carsontpeters-rgb/Racing-Sim/Cad Files/Assemblys/Stick (1).step

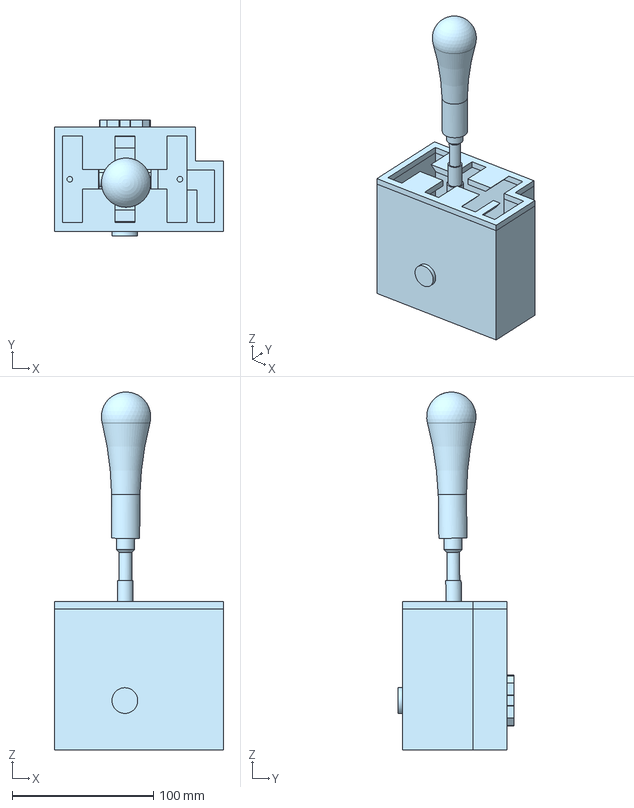
[picture p20: CAD file, 2026-03-14]
Cad Files/Assemblys/Stick (1).step
120.0 x 82.2 x 253.5 mm
