carsontpeters-rgb/Racing-Sim/Cad Files/Control panel/Knobs.step

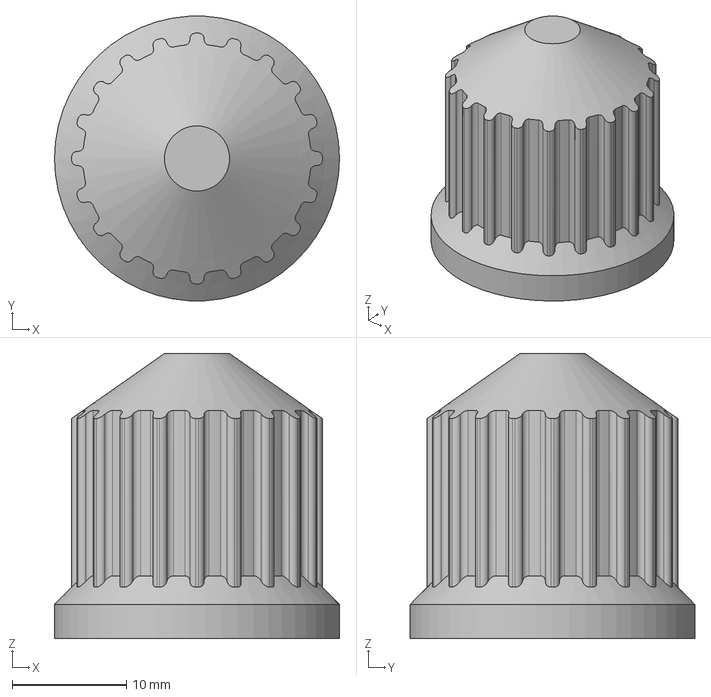
[picture p21: CAD file, 2026-03-14]
Cad Files/Control panel/Knobs.step
25.0 x 25.0 x 25.0 mm
