carsontpeters-rgb/Racing-Sim/Cad Files/Electronics/Rotery encoders.step

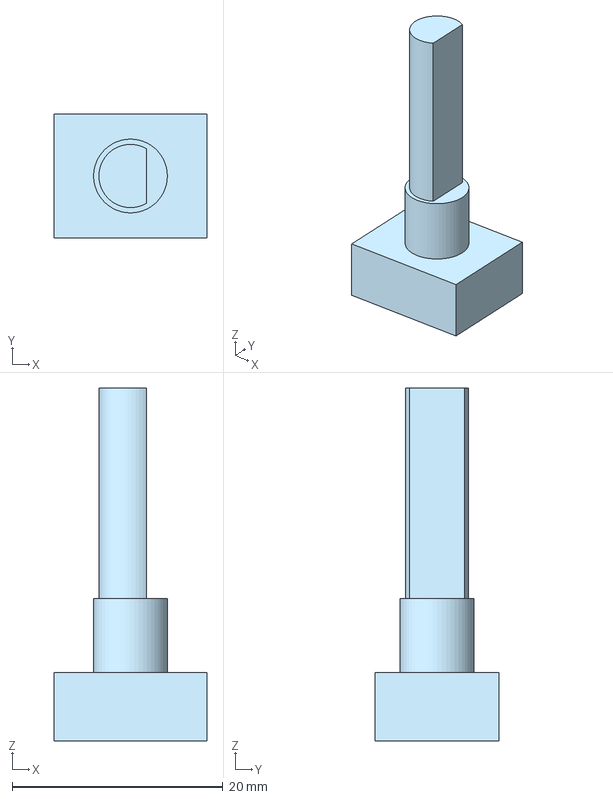
[picture p22: CAD file, 2026-03-14]
Cad Files/Electronics/Rotery encoders.step
14.5 x 11.8 x 33.5 mm
