carsontpeters-rgb/Racing-Sim/Cad Files/None Printed Parts/spring base Mount rod.step

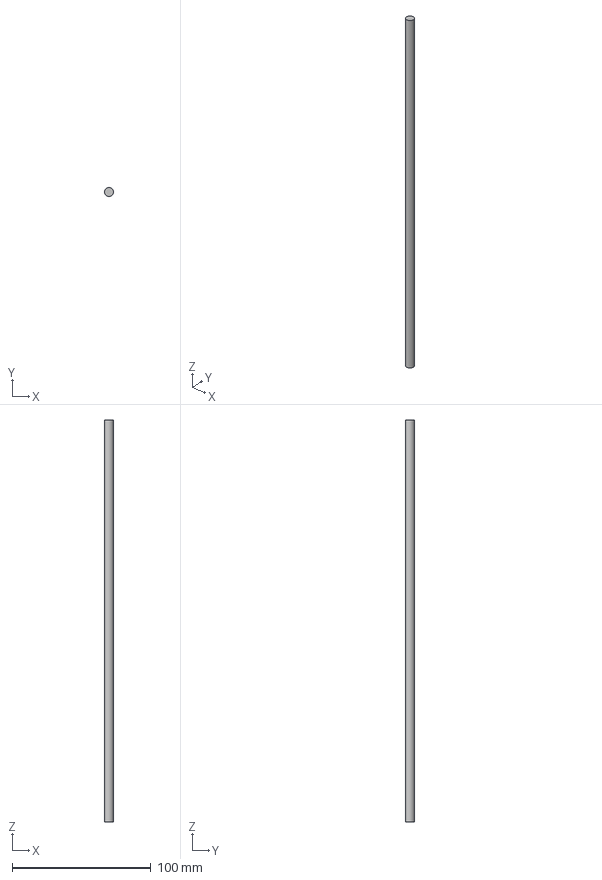
[picture p23: CAD file, 2026-03-14]
Cad Files/None Printed Parts/spring base Mount rod.step
6.49 x 6.50 x 290.0 mm
