carsontpeters-rgb/Racing-Sim/Cad Files/Pedals/Gas, Clutch and Break Pedal.step

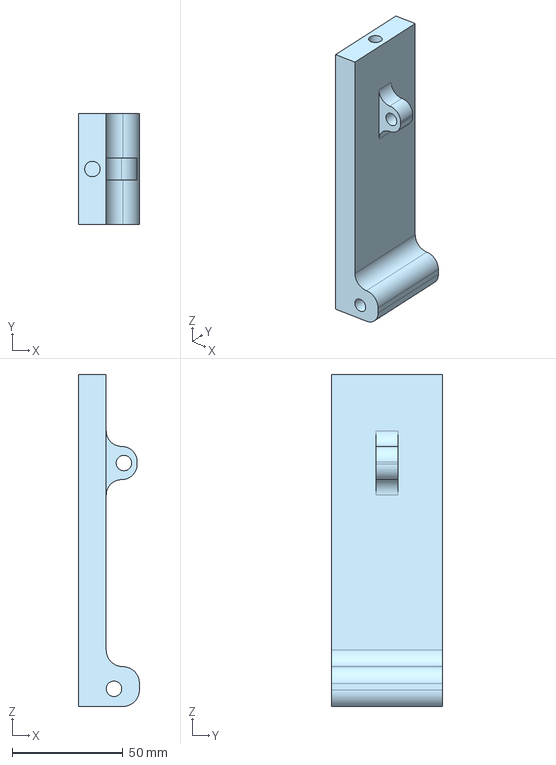
[picture p24: CAD file, 2026-03-14]
Cad Files/Pedals/Gas, Clutch and Break Pedal.step
27.5 x 50.0 x 150.0 mm
