carsontpeters-rgb/Racing-Sim/Cad Files/Shifter/X-AXIS.step

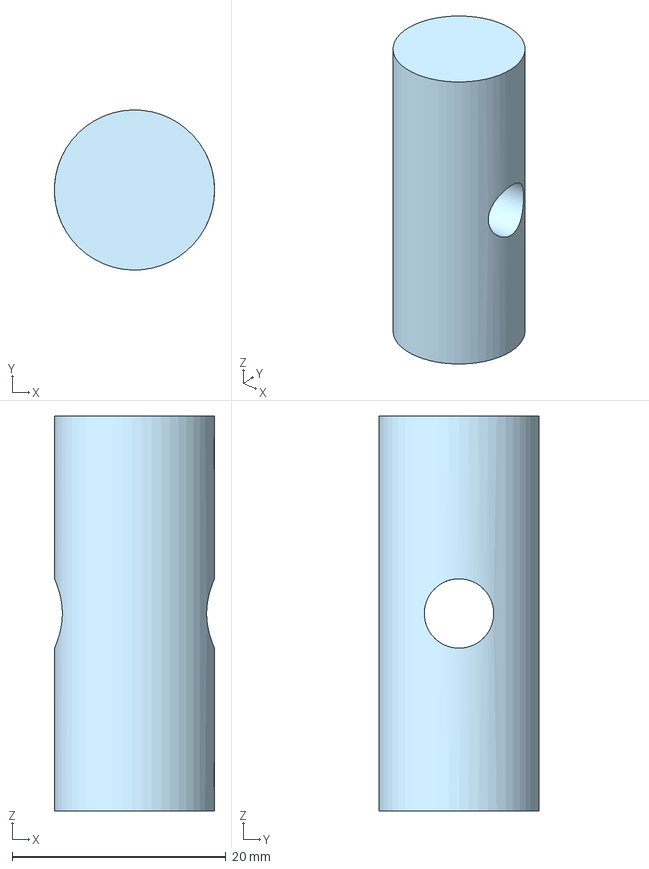
[picture p25: CAD file, 2026-03-14]
Cad Files/Shifter/X-AXIS.step
15.0 x 15.0 x 37.0 mm
