carsontpeters-rgb/Racing-Sim/Cad Files/Steering Wheel/Wheel gear.step

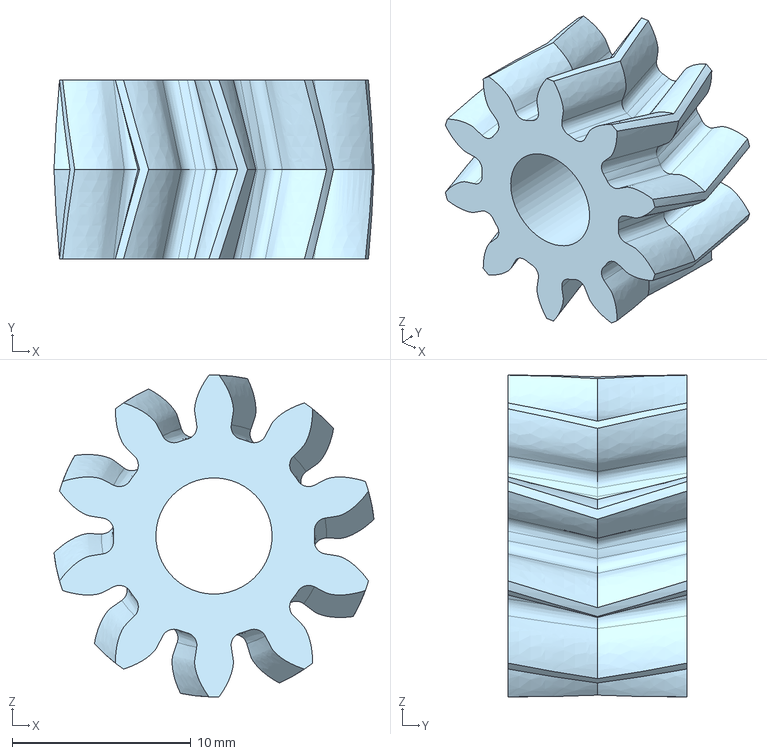
[picture p26: CAD file, 2026-03-14]
Cad Files/Steering Wheel/Wheel gear.step
17.9 x 10.0 x 18.0 mm
