carsontpeters-rgb/Racing-Sim/Cad Files/Assemblys/Pedals.step

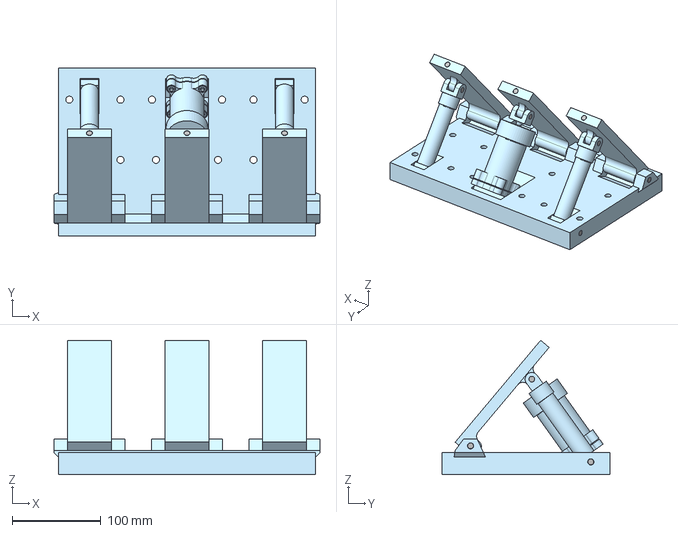
[picture p27: CAD file, 2026-03-14]
Cad Files/Assemblys/Pedals.step
300.0 x 190.0 x 151.6 mm
