carsontpeters-rgb/Racing-Sim/Cad Files/Electronics/Load Cell.step

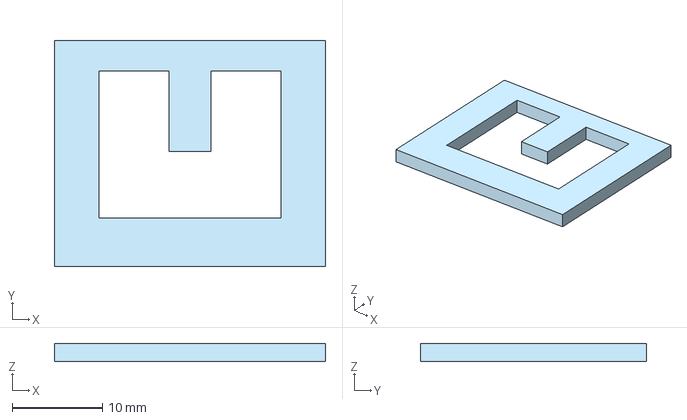
[picture p28: CAD file, 2026-03-14]
Cad Files/Electronics/Load Cell.step
30.0 x 25.0 x 2.00 mm
