carsontpeters-rgb/Racing-Sim/Cad Files/None Printed Parts/Pedal core rod.step

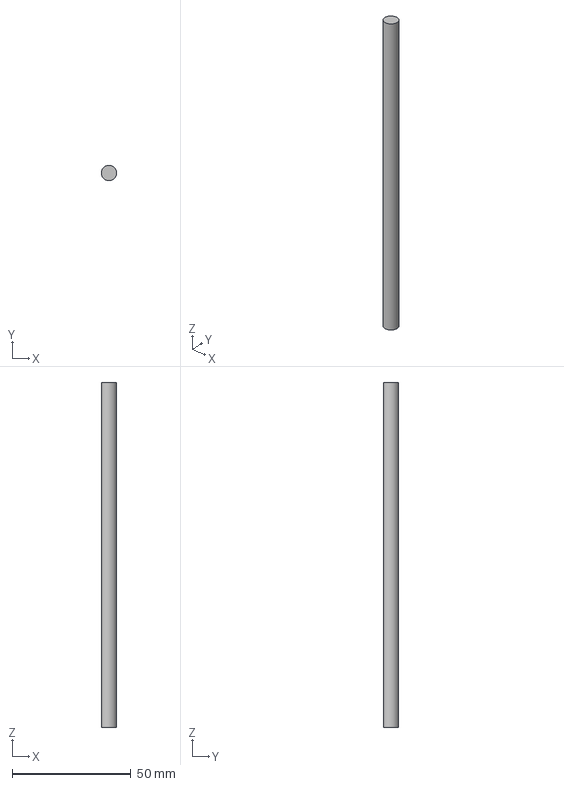
[picture p29: CAD file, 2026-03-14]
Cad Files/None Printed Parts/Pedal core rod.step
6.49 x 6.50 x 145.0 mm
