carsontpeters-rgb/Racing-Sim/Cad Files/Pedals/Cover.step

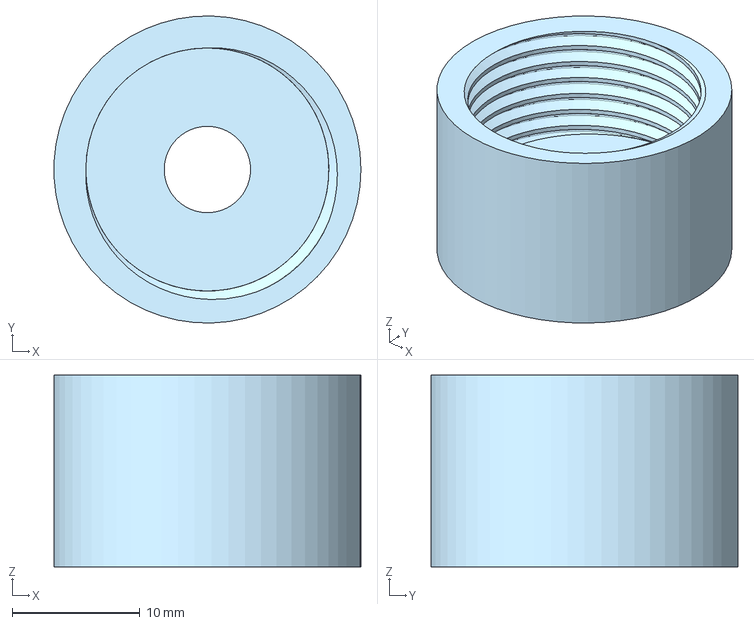
[picture p30: CAD file, 2026-03-14]
Cad Files/Pedals/Cover.step
24.0 x 24.0 x 15.0 mm
