carsontpeters-rgb/Racing-Sim/Cad Files/Shifter/Shifter box.step

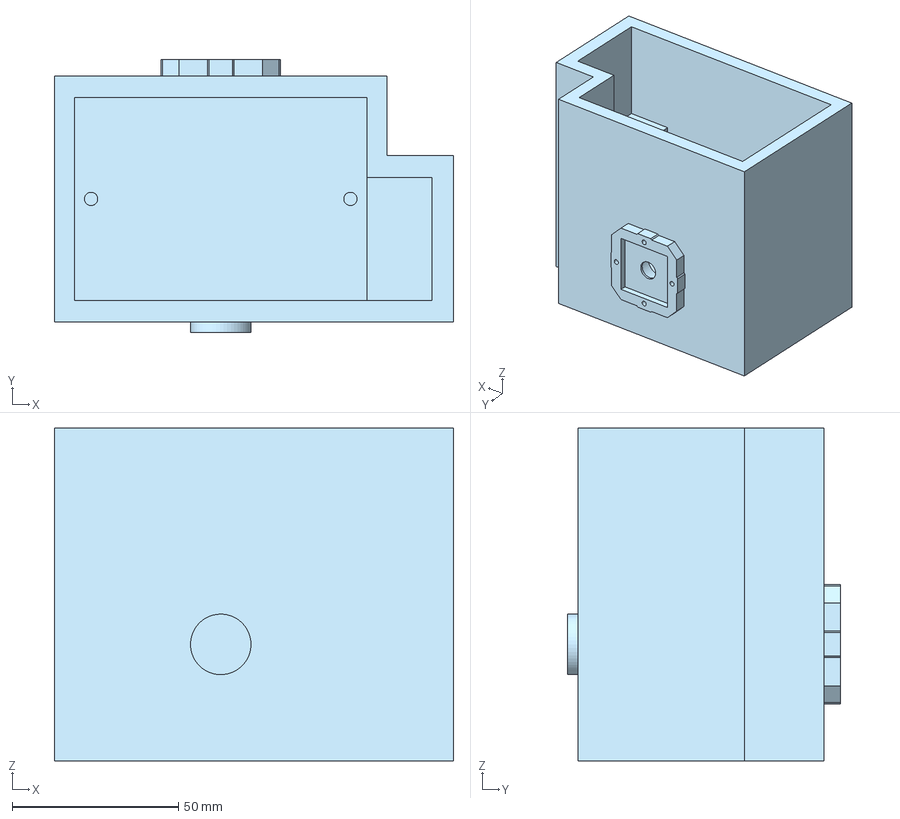
[picture p31: CAD file, 2026-03-14]
Cad Files/Shifter/Shifter box.step
120.0 x 82.2 x 100.0 mm
