carsontpeters-rgb/Racing-Sim/Cad Files/Steering Wheel/Rack.step

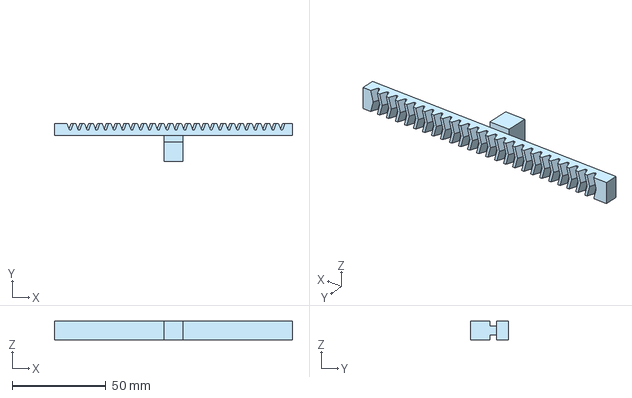
[picture p32: CAD file, 2026-03-14]
Cad Files/Steering Wheel/Rack.step
127.2 x 20.4 x 10.0 mm
