carsontpeters-rgb/Racing-Sim/Cad Files/Electronics/HX711.step

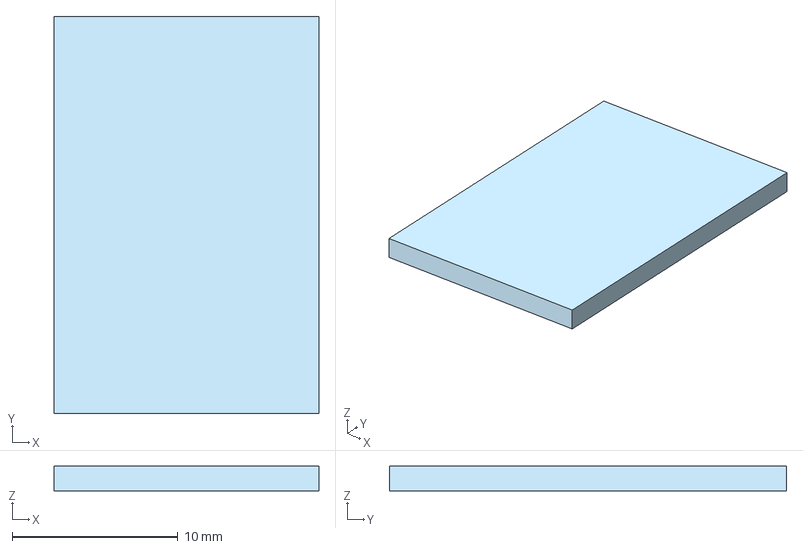
[picture p33: CAD file, 2026-03-14]
Cad Files/Electronics/HX711.step
16.0 x 24.0 x 1.50 mm
