carsontpeters-rgb/Racing-Sim/Cad Files/None Printed Parts/Wheel.step

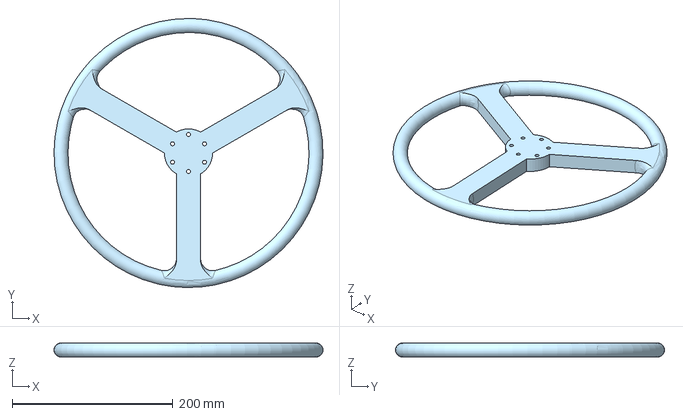
[picture p34: CAD file, 2026-03-14]
Cad Files/None Printed Parts/Wheel.step
335.0 x 335.0 x 17.5 mm
