carsontpeters-rgb/Racing-Sim/Cad Files/Pedals/Pedal Mounts.step

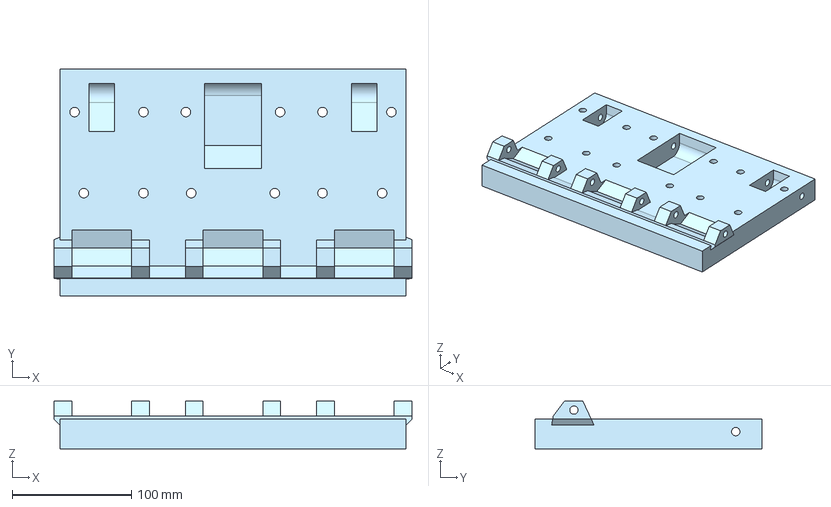
[picture p35: CAD file, 2026-03-14]
Cad Files/Pedals/Pedal Mounts.step
300.0 x 190.0 x 40.0 mm
