carsontpeters-rgb/Racing-Sim/Cad Files/Shifter/H Plate.step

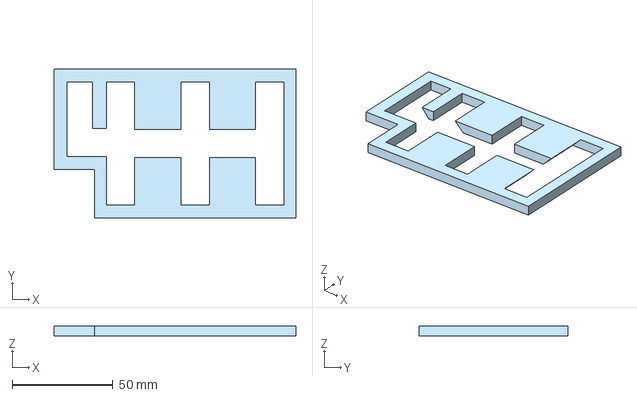
[picture p36: CAD file, 2026-03-14]
Cad Files/Shifter/H Plate.step
120.0 x 74.0 x 5.00 mm
