carsontpeters-rgb/Racing-Sim/Cad Files/Steering Wheel/STEERING HOUSING.step

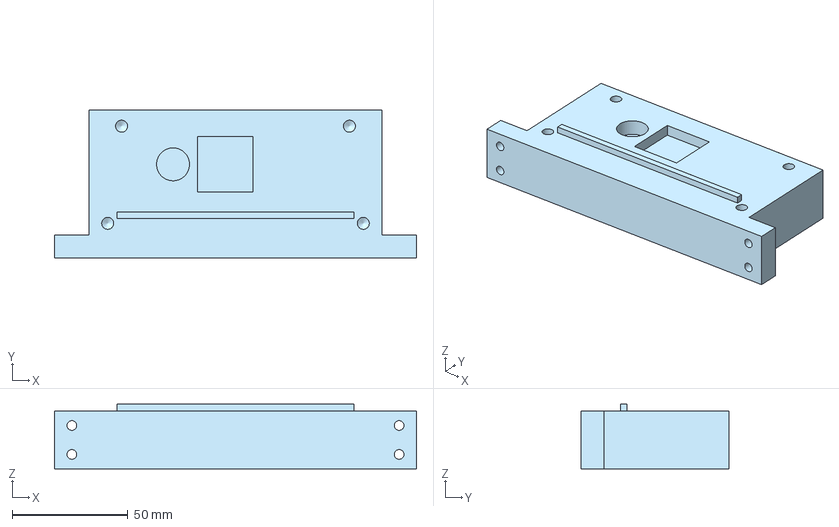
[picture p37: CAD file, 2026-03-14]
Cad Files/Steering Wheel/STEERING HOUSING.step
156.5 x 64.0 x 28.0 mm
