carsontpeters-rgb/Racing-Sim/Cad Files/Electronics/teensy 4.1.step

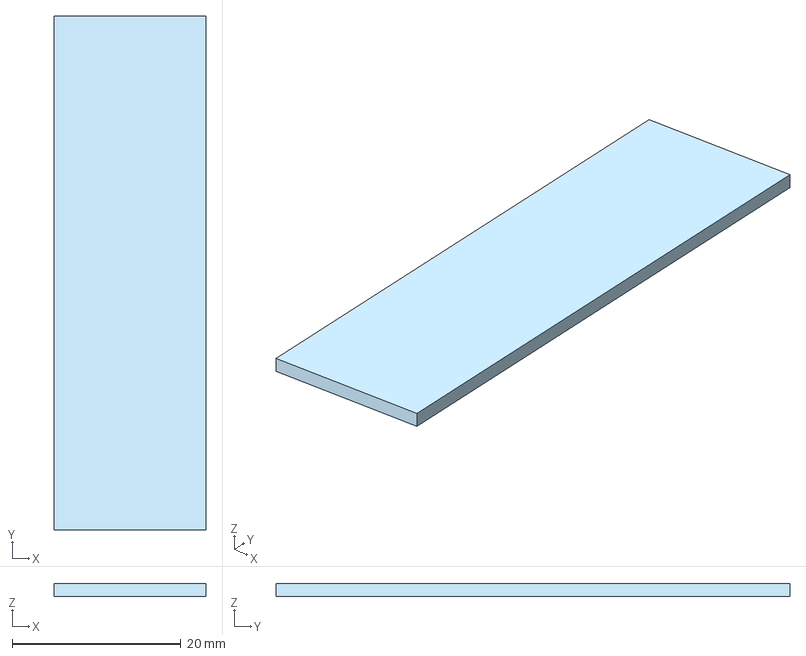
[picture p38: CAD file, 2026-03-14]
Cad Files/Electronics/teensy 4.1.step
18.0 x 61.0 x 1.50 mm
