carsontpeters-rgb/Racing-Sim/Cad Files/None Printed Parts/Pedal Rod.step

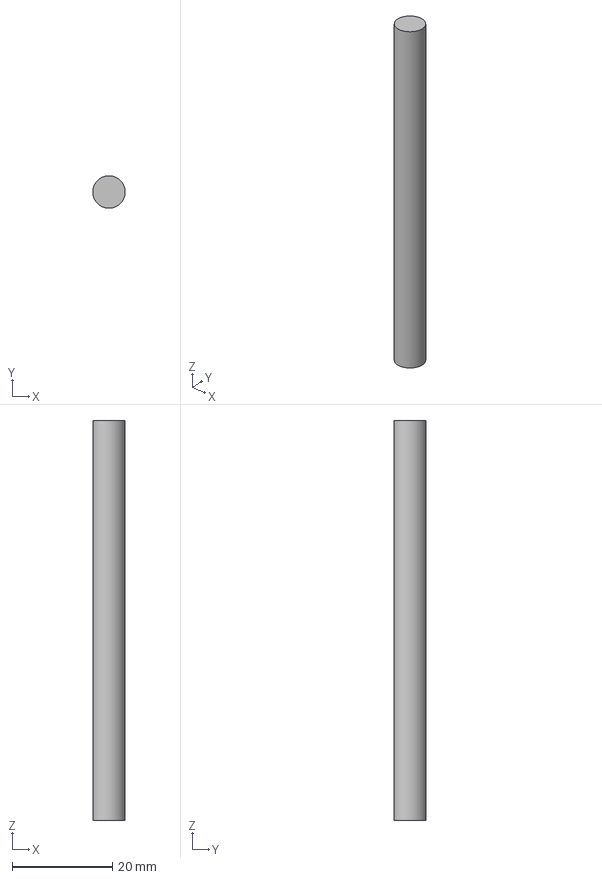
[picture p39: CAD file, 2026-03-14]
Cad Files/None Printed Parts/Pedal Rod.step
6.49 x 6.50 x 80.0 mm
