carsontpeters-rgb/Racing-Sim/Cad Files/Pedals/Spring Cylinder brake.step

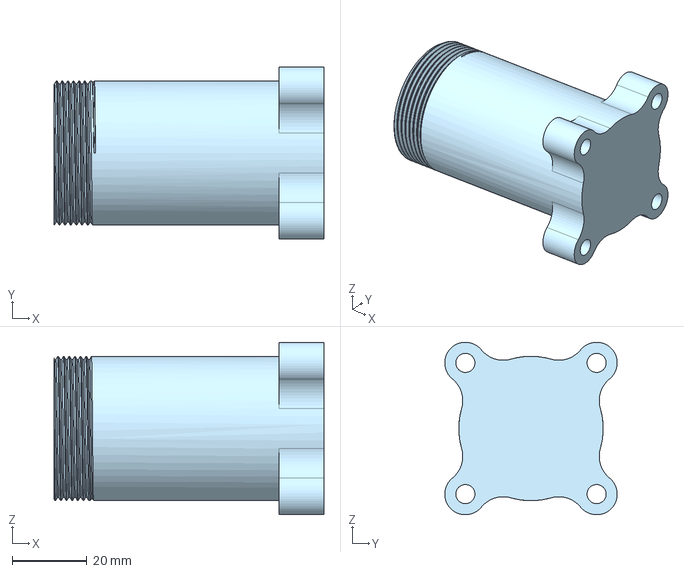
[picture p40: CAD file, 2026-03-14]
Cad Files/Pedals/Spring Cylinder brake.step
72.0 x 46.0 x 46.0 mm
