carsontpeters-rgb/Racing-Sim/Cad Files/Shifter/Resitance peice.step

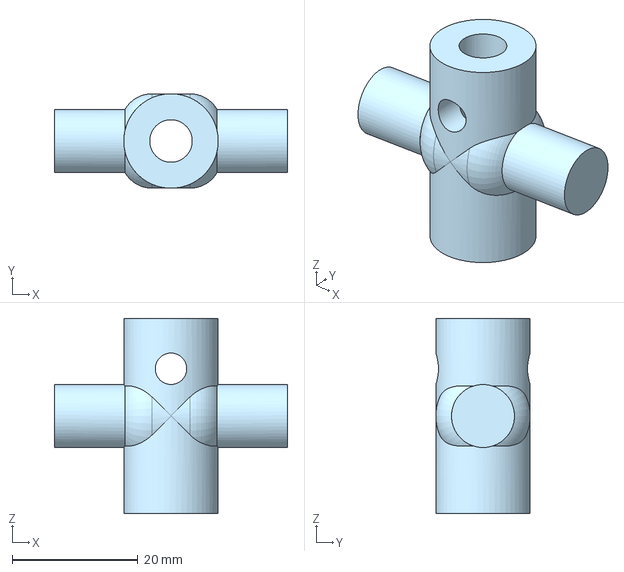
[picture p41: CAD file, 2026-03-14]
Cad Files/Shifter/Resitance peice.step
37.0 x 15.0 x 31.0 mm
