carsontpeters-rgb/Racing-Sim/Cad Files/Electronics/AS5600.step

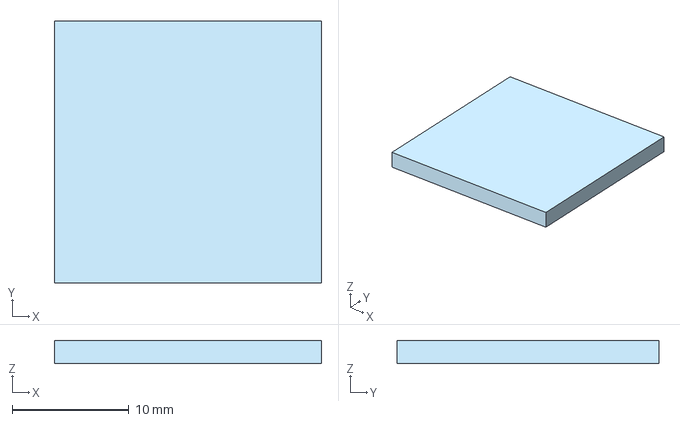
[picture p42: CAD file, 2026-03-14]
Cad Files/Electronics/AS5600.step
22.9 x 22.5 x 2.00 mm
