carsontpeters-rgb/Racing-Sim/Cad Files/None Printed Parts/Bearing.step

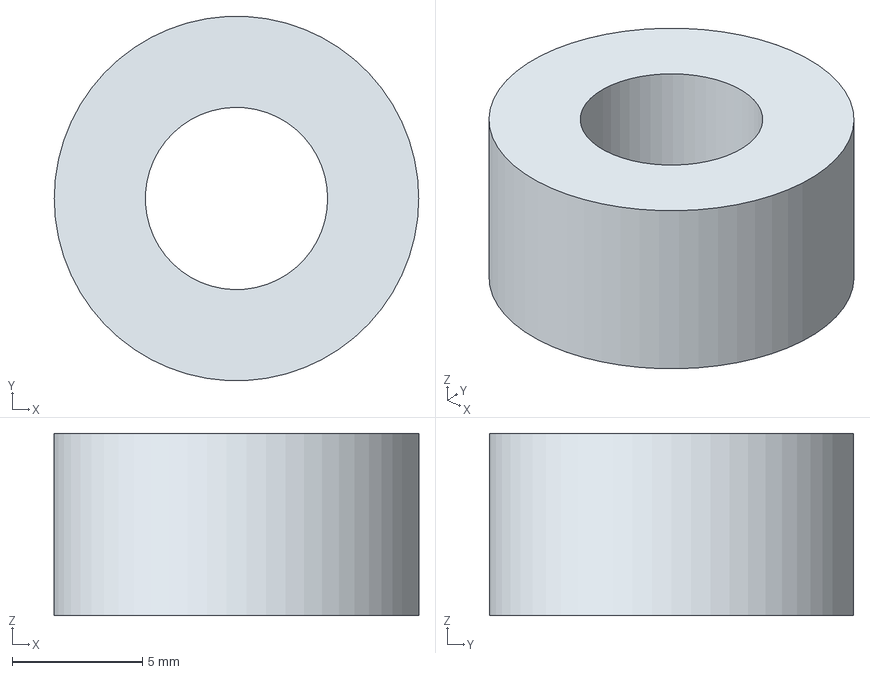
[picture p43: CAD file, 2026-03-14]
Cad Files/None Printed Parts/Bearing.step
14.0 x 14.0 x 7.00 mm
