carsontpeters-rgb/Racing-Sim/Cad Files/Pedals/Brake cover.step

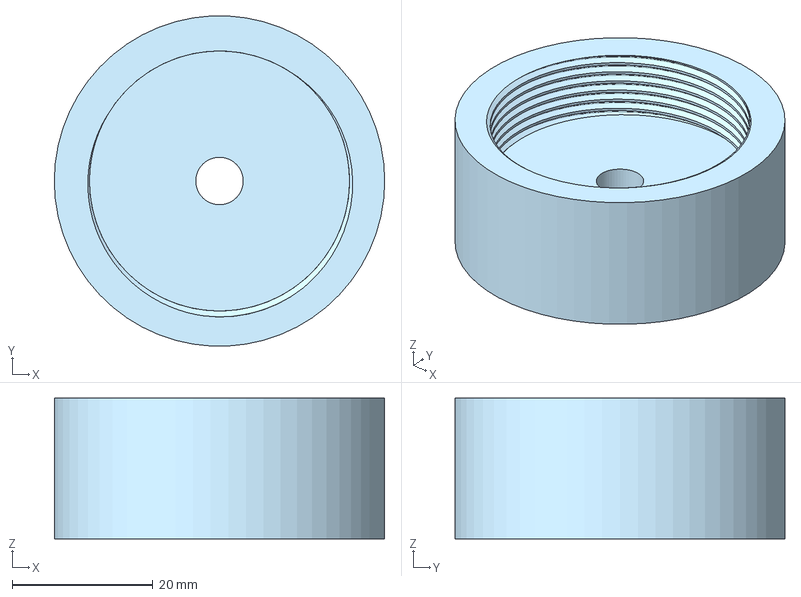
[picture p44: CAD file, 2026-03-14]
Cad Files/Pedals/Brake cover.step
47.0 x 46.9 x 20.0 mm
