carsontpeters-rgb/Racing-Sim/Cad Files/Shifter/rod sleeve.step

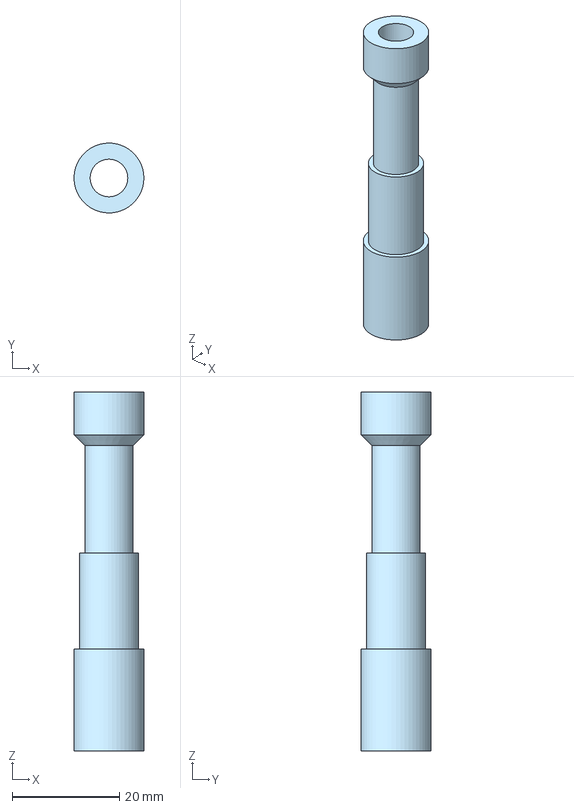
[picture p45: CAD file, 2026-03-14]
Cad Files/Shifter/rod sleeve.step
13.0 x 13.0 x 66.8 mm
