carsontpeters-rgb/Racing-Sim/Cad Files/Electronics/Oled.step

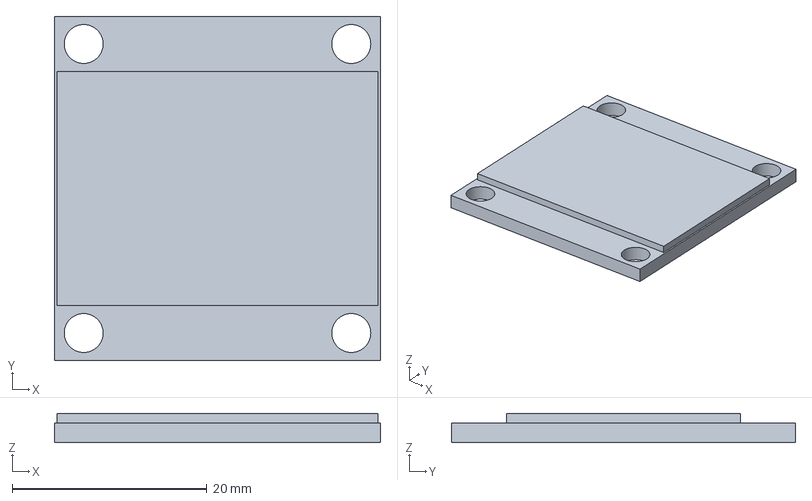
[picture p46: CAD file, 2026-03-14]
Cad Files/Electronics/Oled.step
33.5 x 35.4 x 3.00 mm
