carsontpeters-rgb/Racing-Sim/Cad Files/Pedals/Spring Rod.step

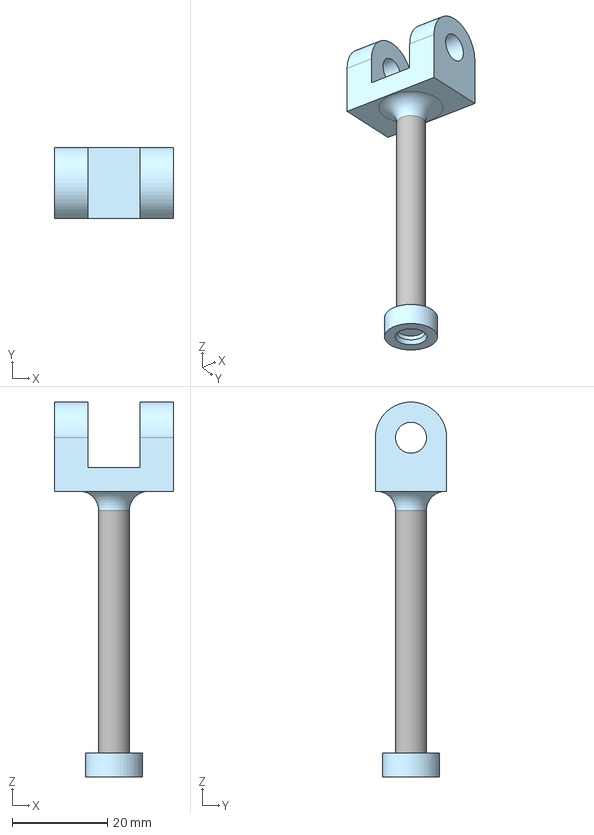
[picture p47: CAD file, 2026-03-14]
Cad Files/Pedals/Spring Rod.step
25.0 x 15.0 x 78.8 mm
