carsontpeters-rgb/Racing-Sim/Cad Files/Shifter/coller.step

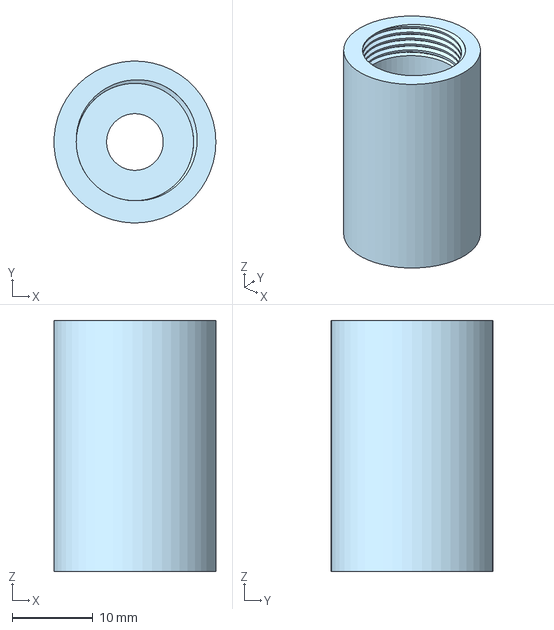
[picture p48: CAD file, 2026-03-14]
Cad Files/Shifter/coller.step
20.0 x 20.0 x 31.0 mm
