carsontpeters-rgb/Racing-Sim/Cad Files/Shifter/Stick.step

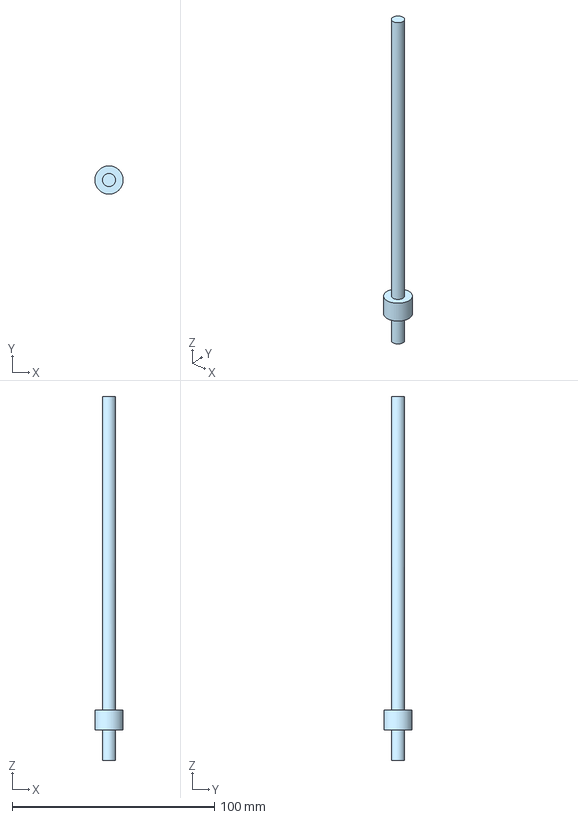
[picture p49: CAD file, 2026-03-14]
Cad Files/Shifter/Stick.step
14.0 x 14.0 x 180.0 mm
