carsontpeters-rgb/Racing-Sim/Cad Files/Pedals/Spring Rod Brake.step

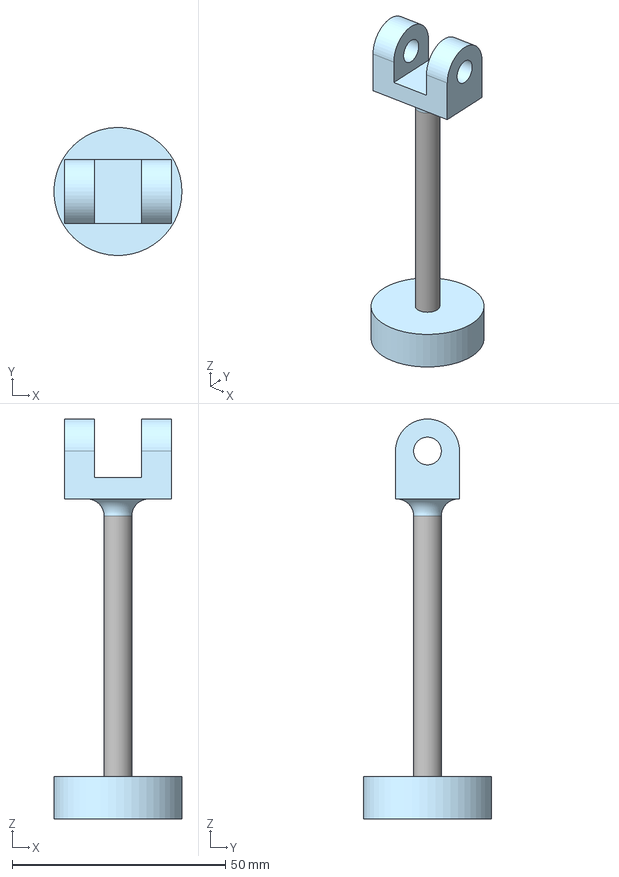
[picture p50: CAD file, 2026-03-14]
Cad Files/Pedals/Spring Rod Brake.step
30.0 x 30.0 x 93.8 mm
